danjoannis/steve/steve_io/util.h

/*
 * util.h
 *
 *  Created on: Nov 1, 2015
 *      Author: Daniel
 */

#ifndef UTIL_H_
#define UTIL_H_

#define TRUE 1
#define FALSE 0

void uart0_itoaWrite(int n);
void my_reverse (char s[]);
int my_strlen(char s[]);


#endif /* UTIL_H_ */
